ArthurFDLR/BlackOut_Challenge/Python_FrontEnd/map.jpg

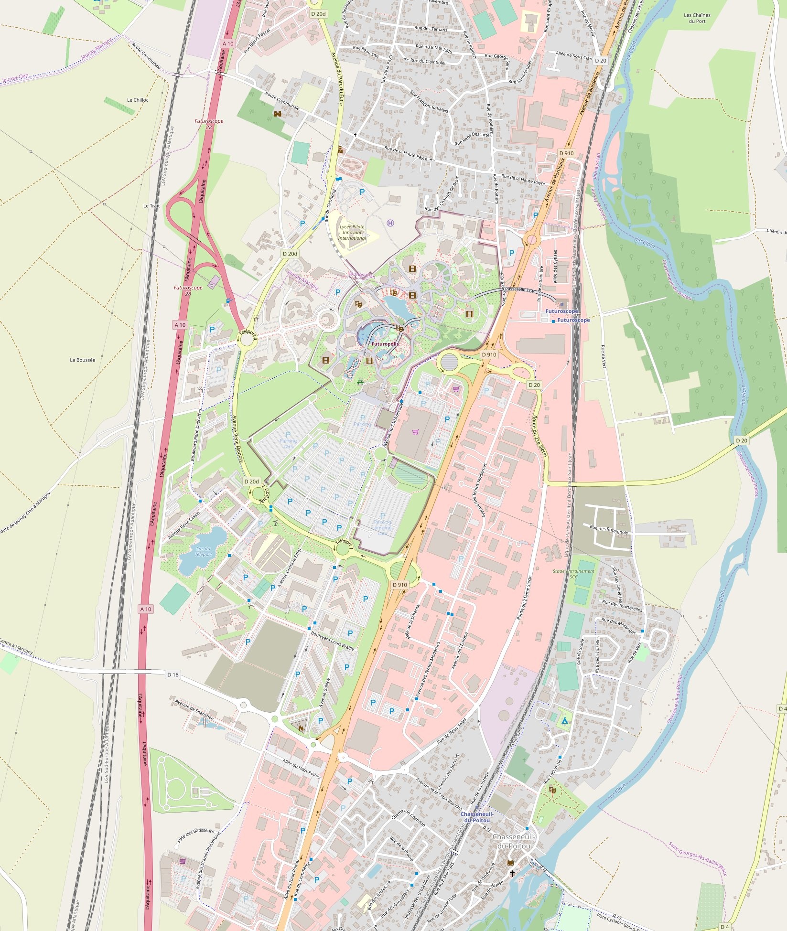
Python_FrontEnd/map.jpg
